telavivmakers/at-tami/shields/diyStepperDriver/half-bridge.asc

C1: cap; 1e-9
D1: diode
D2: diode
D3: diode
D4: diode
D5: diode
D6: diode
D7: diode
D8: diode
M1: pmos; Si1555DL_P
M2: nmos; FDS6961A
Q1: npn
Q2: pnp
R1: res; 1K
R2: res; 10K
R3: res; 10K
R4: res; 1K
R5: res; 1K
R6: res; 10R
R7: res; 1K
R8: res; 1K
R9: res; 10R
V1: voltage; 5V
V2: voltage; 20V
V3: voltage; PULSE(0 5v 0 1us 1us 100us 200us 10)
Named nets: 0
.tran 0 2ms 0
