telavivmakers/at-tami/ATTAMI.brd

## EAGLE design ATTAMI.brd (2014-09-08, an earlier design)

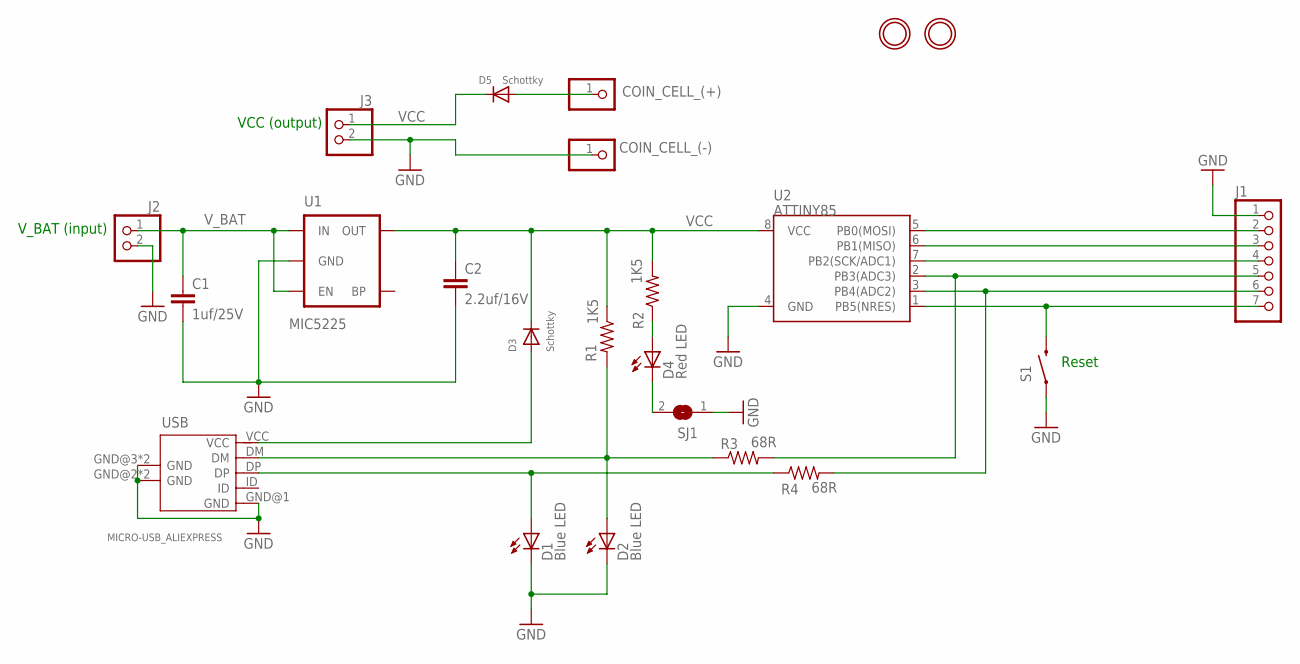
[picture p33: schematic ATTAMI.sch]

Parts:
C1: 1uf/25V; 0805
C2: 2.2uf/16V; 0805
COIN_CELL_(+): PINHD-1X1CB; 1X01-CLEANBIG
COIN_CELL_(-): PINHD-1X1CB; 1X01-CLEANBIG
D1, D2: Blue LED; LED-805
D3, D5: Schottky; SOD-323
D4: Red LED; LED-805
J1: HEADER-1X7ROUND; 1X07_ROUND
J2, J3: HEADER-1X2ROUND; 1X02_ROUND
R1, R2: 1K5; 0805
R3, R4: 68R; 0805
S1: SWITCH-MOMENTARY-2-SMD-1101NE; TACTILE-SWITCH-1101NE
SJ1: SOLDERJUMPERCLOSED; SOLDERJUMPER_CLOSEDWIRE
U1: MIC5225; SOT23-5
U2: ATTINY85; SO08-EIAJ
U$1, U$2: MOUNTINGHOLE2.0; MOUNTINGHOLE_2.0_PLATED
USB: MICRO-USB_ALIEXPRESS; USB-MICRO-ALIEXPRESS

Connections:
GND: C1.2, C2.2, COIN_CELL_(-).1, D1.C, D2.C, J1.1, J2.2, J3.2, S1.P$1 (1), SJ1.1, U1.2 (GND), U2.4 (GND), USB.GND@1 (GND), USB.GND@2 (GND), USB.GND@3 (GND), USB.P$9 (GND), USB.P$10 (GND)
unnamed: J1.5, R3.2, U2.2 (PB3(ADC3))
unnamed: J1.2, U2.5 (PB0(MOSI))
unnamed: COIN_CELL_(+).1, D5.AQ (A)
unnamed: J1.4, U2.7 (PB2(SCK/ADC1))
unnamed: J1.6, R4.2, U2.3 (PB4(ADC2))
unnamed: D1.A, R4.1, USB.DP
unnamed: J1.7, S1.P$2 (2), U2.1 (PB5(NRES))
unnamed: D2.A, R1.2, R3.1, USB.DM
unnamed: D4.A, R2.1
unnamed: D4.C, SJ1.2
unnamed: J1.3, U2.6 (PB1(MISO))
V-BUS: D3.AQ (A), USB.VCC
VCC: C2.1, D3.CQ (C), D5.CQ (C), J3.1, R1.1, R2.2, U1.5 (OUT), U2.8 (VCC)
V_BAT: C1.1, J2.1, U1.1 (IN), U1.3 (EN)

Notes on the sheet:
VCC (output)
V_BAT (input)
Reset

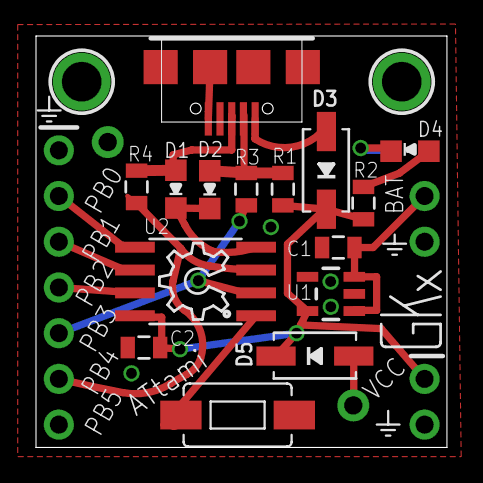
[picture p34: board ATTAMI.brd from above]

Board: 2 copper layers, 22.8 x 22.9 mm, 24 parts (1 on the bottom side), 15 nets.

Other parts of the board:
U$3: OSHW_6X150_NOTEXT
